specadmin/sauna-control/photos/photo_2020-05-21_22-15-29.jpg

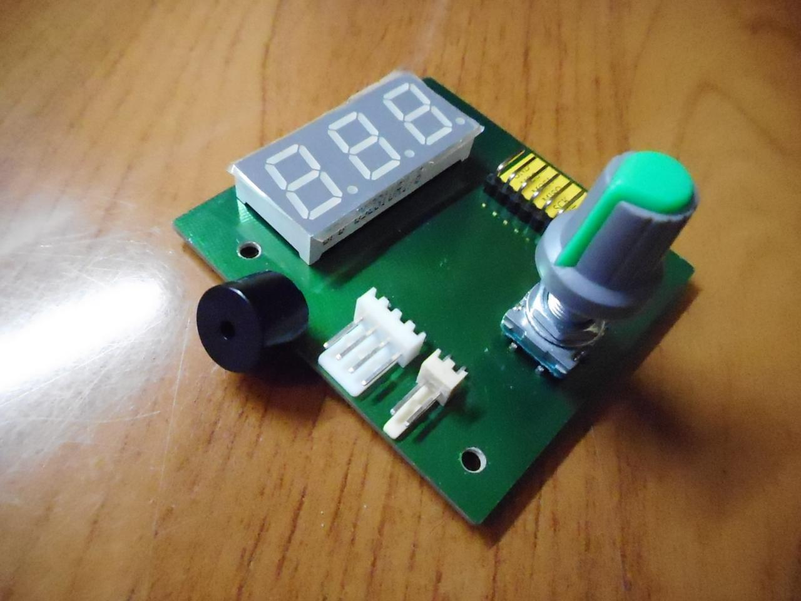
photos/photo_2020-05-21_22-15-29.jpg
